mariacthi/Rust-Music-Player---Proiect-PM/kicad_sch.kicad_pcb

## KiCad design hardware/sport_bike_conn/sport_bike_conn.kicad_sch

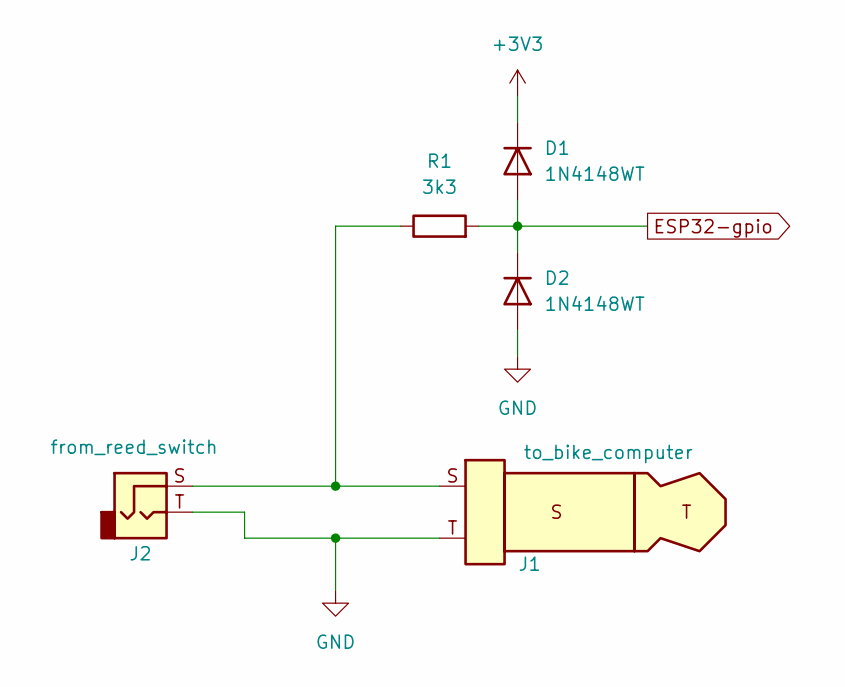
[picture p4: schematic sport_bike_conn.kicad_sch]

Parts:
D1, D2: 1N4148WT; D_SOD-523
J1: to_bike_computer
J2: from_reed_switch
R1: 3k3

Connections:
+3V3: D1.1 (K)
ESP32-gpio: D1.2 (A), D2.1 (K), R1.2
GND: D2.2 (A), J1.T, J2.T
unnamed: J1.S, J2.S, R1.1
